westonb/little-bee-B1/modeling/trace_1_6mm_plt.png

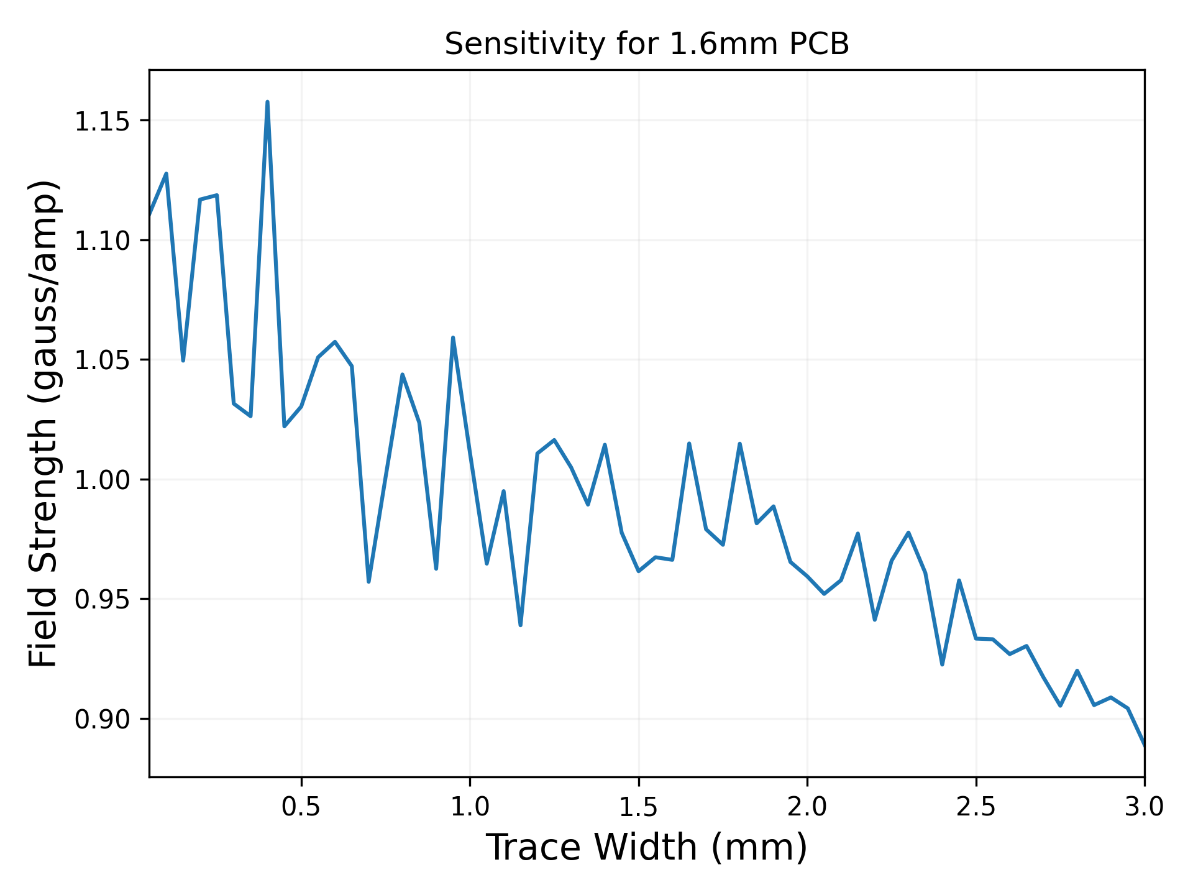
modeling/trace_1_6mm_plt.png
