westonb/little-bee-B1/production/test-data/A02.CSV

in Sa | Frequency in Hz | Gain in dB | Phase in ° | Amplitude in Vpp
1.00E+00 | 1.000E+05 | -1.487E-01 | 5.466E-02 | 2.500E+00
2.00E+00 | 1.047E+05 | -1.316E-01 | 8.698E-02 | 2.500E+00
3.00E+00 | 1.096E+05 | -1.391E-01 | 3.220E-02 | 2.500E+00
4.00E+00 | 1.148E+05 | -1.309E-01 | 1.892E-02 | 2.500E+00
5.00E+00 | 1.202E+05 | -1.388E-01 | 3.974E-02 | 2.500E+00
6.00E+00 | 1.259E+05 | -1.266E-01 | -5.883E-02 | 2.500E+00
7.00E+00 | 1.318E+05 | -1.180E-01 | -1.561E-01 | 2.500E+00
8.00E+00 | 1.380E+05 | -1.381E-01 | -5.508E-03 | 2.500E+00
9.00E+00 | 1.445E+05 | -1.184E-01 | 2.692E-02 | 2.500E+00
1.00E+01 | 1.514E+05 | -1.447E-01 | 6.229E-02 | 2.500E+00
1.10E+01 | 1.585E+05 | -1.110E-01 | -1.320E-02 | 2.500E+00
1.20E+01 | 1.660E+05 | -1.207E-01 | -2.107E-02 | 2.500E+00
1.30E+01 | 1.738E+05 | -1.284E-01 | 2.531E-02 | 2.500E+00
1.40E+01 | 1.820E+05 | -1.277E-01 | 8.084E-02 | 2.500E+00
1.50E+01 | 1.905E+05 | -1.227E-01 | 4.457E-02 | 2.500E+00
1.60E+01 | 1.995E+05 | -1.220E-01 | 2.908E-02 | 2.500E+00
1.70E+01 | 2.089E+05 | -1.032E-01 | 1.429E-01 | 2.500E+00
1.80E+01 | 2.188E+05 | -1.187E-01 | 1.117E-01 | 2.500E+00
1.90E+01 | 2.291E+05 | -1.160E-01 | 8.492E-02 | 2.500E+00
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
