westonb/little-bee-B1/production/test-data/A03.CSV

in Sa | Frequency in Hz | Gain in dB | Phase in ° | Amplitude in Vpp
1.00E+00 | 1.000E+05 | 1.248E-01 | -1.595E-01 | 2.500E+00
2.00E+00 | 1.047E+05 | 1.341E-01 | -1.022E-01 | 2.500E+00
3.00E+00 | 1.096E+05 | 1.454E-01 | -1.226E-01 | 2.500E+00
4.00E+00 | 1.148E+05 | 1.388E-01 | -1.257E-01 | 2.500E+00
5.00E+00 | 1.202E+05 | 1.369E-01 | -1.778E-01 | 2.500E+00
6.00E+00 | 1.259E+05 | 1.383E-01 | -1.327E-01 | 2.500E+00
7.00E+00 | 1.318E+05 | 1.203E-01 | -1.649E-01 | 2.500E+00
8.00E+00 | 1.380E+05 | 1.291E-01 | -1.898E-01 | 2.500E+00
9.00E+00 | 1.445E+05 | 1.390E-01 | -2.317E-01 | 2.500E+00
1.00E+01 | 1.514E+05 | 1.421E-01 | -2.449E-01 | 2.500E+00
1.10E+01 | 1.585E+05 | 1.318E-01 | -2.079E-01 | 2.500E+00
1.20E+01 | 1.660E+05 | 1.502E-01 | -2.013E-01 | 2.500E+00
1.30E+01 | 1.738E+05 | 1.421E-01 | -1.844E-01 | 2.500E+00
1.40E+01 | 1.820E+05 | 1.386E-01 | -2.586E-01 | 2.500E+00
1.50E+01 | 1.905E+05 | 1.413E-01 | -1.765E-01 | 2.500E+00
1.60E+01 | 1.995E+05 | 1.335E-01 | -1.859E-01 | 2.500E+00
1.70E+01 | 2.089E+05 | 1.386E-01 | -1.541E-01 | 2.500E+00
1.80E+01 | 2.188E+05 | 1.572E-01 | -1.150E-01 | 2.500E+00
1.90E+01 | 2.291E+05 | 1.382E-01 | -1.577E-01 | 2.500E+00
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
