westonb/little-bee-B1/production/test-data/A04.CSV

in Sa | Frequency in Hz | Gain in dB | Phase in ° | Amplitude in Vpp
1.00E+00 | 1.000E+05 | 2.413E-01 | 2.287E-01 | 2.500E+00
2.00E+00 | 1.047E+05 | 2.412E-01 | 2.968E-01 | 2.500E+00
3.00E+00 | 1.096E+05 | 2.443E-01 | 2.499E-01 | 2.500E+00
4.00E+00 | 1.148E+05 | 2.456E-01 | 3.993E-01 | 2.500E+00
5.00E+00 | 1.202E+05 | 2.478E-01 | 3.165E-01 | 2.500E+00
6.00E+00 | 1.259E+05 | 2.569E-01 | 2.958E-01 | 2.500E+00
7.00E+00 | 1.318E+05 | 2.580E-01 | 3.229E-01 | 2.500E+00
8.00E+00 | 1.380E+05 | 2.516E-01 | 2.751E-01 | 2.500E+00
9.00E+00 | 1.445E+05 | 2.488E-01 | 4.030E-01 | 2.500E+00
1.00E+01 | 1.514E+05 | 2.539E-01 | 4.150E-01 | 2.500E+00
1.10E+01 | 1.585E+05 | 2.609E-01 | 3.548E-01 | 2.500E+00
1.20E+01 | 1.660E+05 | 2.547E-01 | 3.264E-01 | 2.500E+00
1.30E+01 | 1.738E+05 | 2.608E-01 | 3.737E-01 | 2.500E+00
1.40E+01 | 1.820E+05 | 2.523E-01 | 3.107E-01 | 2.500E+00
1.50E+01 | 1.905E+05 | 2.555E-01 | 3.552E-01 | 2.500E+00
1.60E+01 | 1.995E+05 | 2.543E-01 | 3.851E-01 | 2.500E+00
1.70E+01 | 2.089E+05 | 2.727E-01 | 3.531E-01 | 2.500E+00
1.80E+01 | 2.188E+05 | 2.844E-01 | 3.841E-01 | 2.500E+00
1.90E+01 | 2.291E+05 | 2.810E-01 | 4.080E-01 | 2.500E+00
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
