westonb/little-bee-B1/production/test-data/A05.CSV

in Sa | Frequency in Hz | Gain in dB | Phase in ° | Amplitude in Vpp
1.00E+00 | 1.000E+05 | 2.060E-01 | 5.501E-01 | 2.500E+00
2.00E+00 | 1.047E+05 | 2.061E-01 | 4.706E-01 | 2.500E+00
3.00E+00 | 1.096E+05 | 2.003E-01 | 4.892E-01 | 2.500E+00
4.00E+00 | 1.148E+05 | 2.147E-01 | 5.471E-01 | 2.500E+00
5.00E+00 | 1.202E+05 | 2.158E-01 | 4.609E-01 | 2.500E+00
6.00E+00 | 1.259E+05 | 2.271E-01 | 6.172E-01 | 2.500E+00
7.00E+00 | 1.318E+05 | 2.323E-01 | 5.899E-01 | 2.500E+00
8.00E+00 | 1.380E+05 | 2.329E-01 | 5.954E-01 | 2.500E+00
9.00E+00 | 1.445E+05 | 2.265E-01 | 5.406E-01 | 2.500E+00
1.00E+01 | 1.514E+05 | 2.513E-01 | 5.550E-01 | 2.500E+00
1.10E+01 | 1.585E+05 | 2.406E-01 | 5.758E-01 | 2.500E+00
1.20E+01 | 1.660E+05 | 2.623E-01 | 5.471E-01 | 2.500E+00
1.30E+01 | 1.738E+05 | 2.500E-01 | 5.961E-01 | 2.500E+00
1.40E+01 | 1.820E+05 | 2.725E-01 | 5.563E-01 | 2.500E+00
1.50E+01 | 1.905E+05 | 2.605E-01 | 5.679E-01 | 2.500E+00
1.60E+01 | 1.995E+05 | 2.565E-01 | 5.279E-01 | 2.500E+00
1.70E+01 | 2.089E+05 | 2.728E-01 | 6.247E-01 | 2.500E+00
1.80E+01 | 2.188E+05 | 2.719E-01 | 5.895E-01 | 2.500E+00
1.90E+01 | 2.291E+05 | 2.815E-01 | 6.577E-01 | 2.500E+00
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
