westonb/little-bee-B1/sim/amplifier.asc

C1: cap; 10p
C2: cap; 0.5p
C3: cap; 0.1p
C4: cap; 22p
C5: cap; 120p
C6: cap; 5p
C8: cap; 10p
C9: cap; 0.5p
C10: cap; 0.1p
C11: cap; 750p
C12: cap; 120p
C13: cap; 5p
C15: cap; 10p
C16: cap; 0.5p
C17: cap; 0.1p
C18: cap; 750p
C19: cap; 10p
C20: cap; 0.5p
C21: cap; 0.1p
C22: cap; 22p
C23: cap; 120p
C24: cap; 5p
C26: cap; 120p
C27: cap; 5p
C29: cap; 10p
C30: cap; 0.5p
C31: cap; 0.1p
C32: cap; 22p
C33: cap; 120p
C34: cap; 5p
C36: cap; 10p
C37: cap; 0.5p
C38: cap; 0.1p
C39: cap; 22p
C40: cap; 120p
C41: cap; 5p
C43: cap; 10p
C44: cap; 0.5p
C45: cap; 0.1p
C46: cap; 750p
C47: cap; 120p
C48: cap; 5p
C50: cap; 10p
C51: cap; 0.5p
C52: cap; 0.1p
C53: cap; 750p
C54: cap; 120p
C55: cap; 5p
R1: res; 400
R2: res; 400
R3: res; 1449
R4: res; 105
R5: res; 50
R6: res; 50
R7: res; 105
R8: res; 220
R9: res; 43
R10: res; 1Meg
R11: res; 1.43k
R12: res; 470
R13: res; 400
R14: res; 400
R15: res; 1449
R16: res; 105
R17: res; 50
R18: res; 50
R19: res; 105
R20: res; 220
R21: res; 43
R22: res; 1Meg
R23: res; 3
R24: res; 470
R25: res; 400
R26: res; 400
R27: res; 1449
R28: res; 105
R29: res; 50
R30: res; 50
R31: res; 105
R32: res; 220
R33: res; 43
R34: res; 400
R35: res; 400
R36: res; 1449
R37: res; 105
R38: res; 50
R39: res; 50
R40: res; 105
R41: res; 220
R42: res; 3
R43: res; 470
R44: res; 43
R45: res; 1Meg
R46: res; 1Meg
R47: res; 1.43k
R48: res; 470
R49: res; 400
R50: res; 400
R51: res; 3297
R52: res; 105
R53: res; 50
R54: res; 50
R55: res; 105
R56: res; 220
R57: res; 43
R58: res; 1Meg
R59: res; 3
R60: res; 470
R61: res; 400
R62: res; 400
R63: res; 3297
R64: res; 105
R65: res; 50
R66: res; 50
R67: res; 105
R68: res; 220
R69: res; 43
R70: res; 1Meg
R71: res; 1.43k
R72: res; 470
R73: res; 400
R74: res; 400
R75: res; 3297
R76: res; 105
R77: res; 50
R78: res; 50
R79: res; 105
R80: res; 220
R81: res; 43
R82: res; 1Meg
R83: res; 3
R84: res; 470
R85: res; 400
R86: res; 400
R87: res; 3297
R88: res; 105
R89: res; 50
R90: res; 50
R91: res; 105
R92: res; 220
R93: res; 43
R94: res; 1Meg
R95: res; 1.43k
R96: res; 470
U1: AD8129
U2: opamp2; TLV354
U3: AD8129
U4: opamp2; TLV354
U5: AD8129
U6: opamp2; TLV354
U7: AD8129
U8: opamp2; TLV354
U9: AD8129
U10: opamp2; TLV354
U11: AD8129
U12: opamp2; TLV354
U13: AD8129
U14: opamp2; TLV354
U15: AD8129
U16: opamp2; TLV354
V1: voltage; 2.5
V2: voltage; 2.5
V3: voltage; AC 0.5
V4: voltage; AC 0.5
V5: voltage; AC 0.5
V6: voltage; AC 0.5
V7: voltage; AC 0.5
V8: voltage; AC 0.5
V9: voltage; AC 0.5
V10: voltage; AC 0.5
V11: voltage; AC 0.5
V12: voltage; AC 0.5
V13: voltage; AC 0.5
V14: voltage; AC 0.5
V15: voltage; AC 0.5
V16: voltage; AC 0.5
V17: voltage; AC 0.5
V18: voltage; AC 0.5
Named nets: 0, +2.5V, -2.5V
Poor Model of HMC1041Z Sensor
There is inductive pickup which extends HF range
parasitic PCB capacitances
Analog Switch Capacitance
1M of RG174 coax + scope input impedance
Poor Model of HMC1041Z Sensor
There is inductive pickup which extends HF range
parasitic PCB capacitances
Analog Switch Capacitance
1M of RG174 coax + scope input impedance
Poor Model of HMC1041Z Sensor
There is inductive pickup which extends HF range
parasitic PCB capacitances
Analog Switch Capacitance
1M of RG174 coax + scope input impedance
Poor Model of HMC1041Z Sensor
There is inductive pickup which extends HF range
parasitic PCB capacitances
Analog Switch Capacitance
1M of RG174 coax + scope input impedance
Poor Model of HMC1041Z Sensor
There is inductive pickup which extends HF range
parasitic PCB capacitances
Analog Switch Capacitance
1M of RG174 coax + scope input impedance
Poor Model of HMC1041Z Sensor
There is inductive pickup which extends HF range
parasitic PCB capacitances
Analog Switch Capacitance
1M of RG174 coax + scope input impedance
Poor Model of HMC1041Z Sensor
There is inductive pickup which extends HF range
parasitic PCB capacitances
Analog Switch Capacitance
1M of RG174 coax + scope input impedance
Poor Model of HMC1041Z Sensor
There is inductive pickup which extends HF range
parasitic PCB capacitances
Analog Switch Capacitance
1M of RG174 coax + scope input impedance
Min Sensor Gain, high bandwidth, low output gain
Min Sensor Gain, high bandwidth, high output gain
Min Sensor Gain, low bandwidth, low output gain
Min Sensor Gain, low bandwidth, high output gain
Max Sensor Gain, high bandwidth, low output gain
Max Sensor Gain, high bandwidth, high output gain
Max Sensor Gain, low bandwidth, low output gain
Max Sensor Gain, low bandwidth, high output gain
.INC TLV354.LIB
.INC ad8129.CIR
.ac dec 100 1k 100E6
